kchristidis/watchtower/screenshots/new-module.png

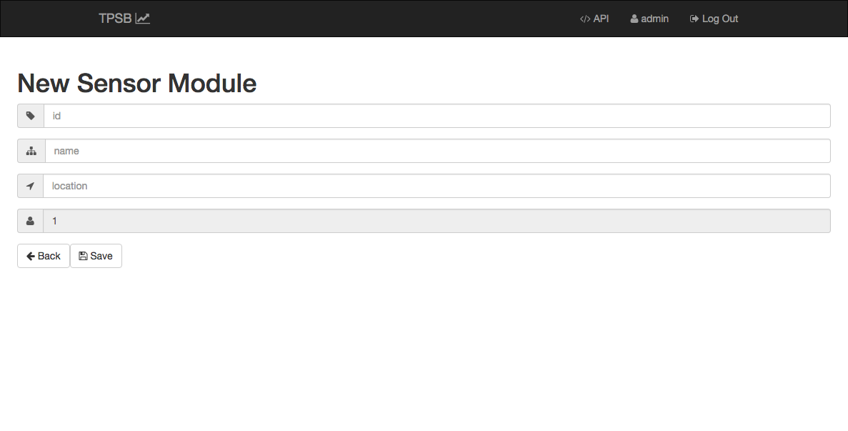
screenshots/new-module.png
